loretod/Braille_Trainer/images/IMG-5150.jpg

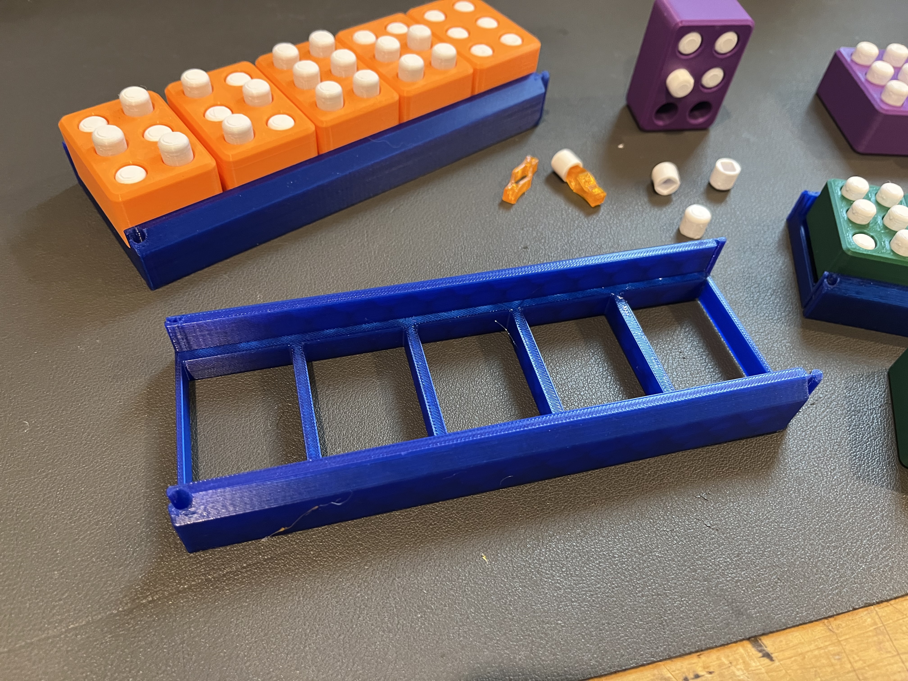
images/IMG-5150.jpg
