loretod/Braille_Trainer/images/IMG-5151.jpg

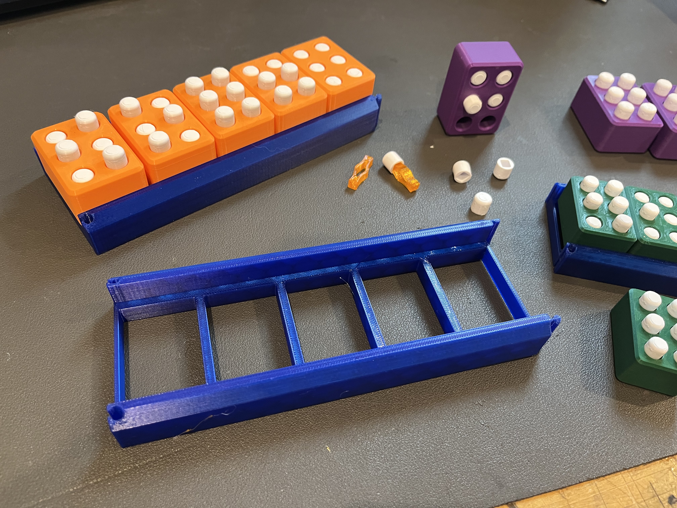
images/IMG-5151.jpg
