loretod/Braille_Trainer/images/IMG-5152.jpg

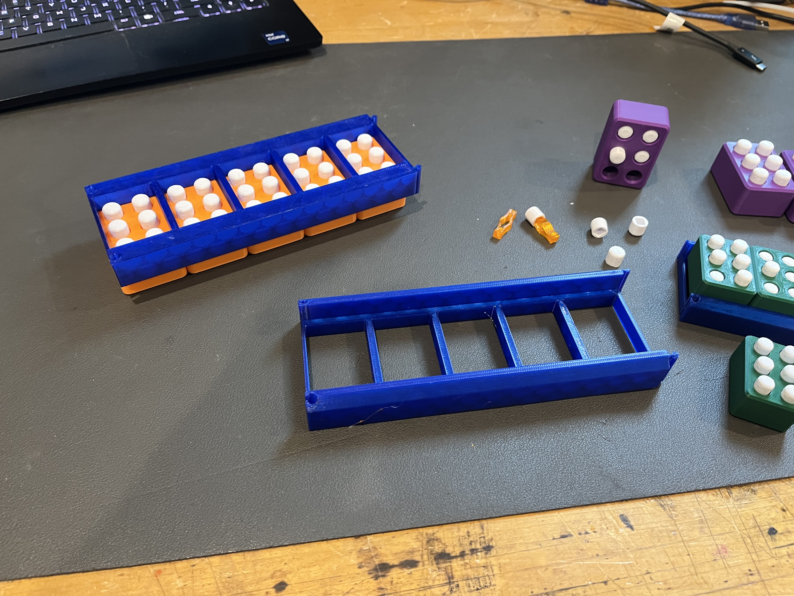
images/IMG-5152.jpg
