loretod/Braille_Trainer/images/IMG-5153.jpg

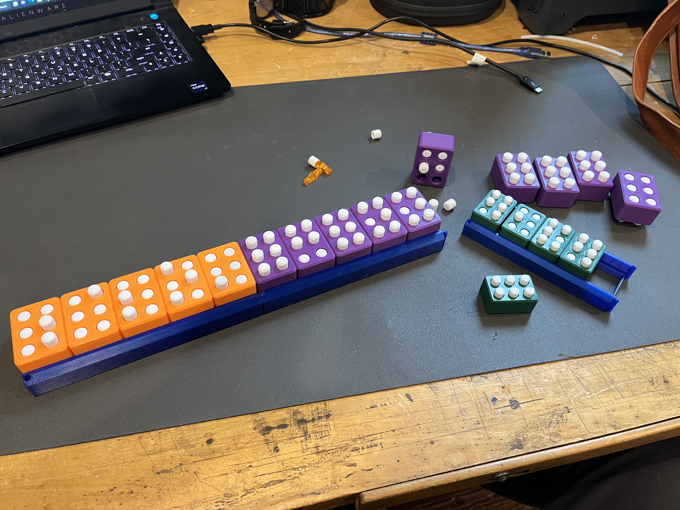
images/IMG-5153.jpg
