loretod/Braille_Trainer/images/IMG-5154.jpg

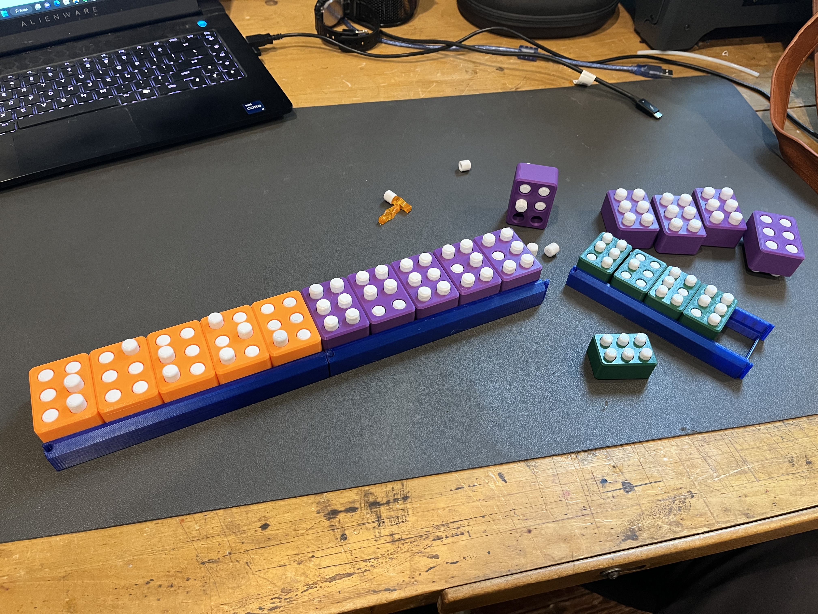
images/IMG-5154.jpg
