loretod/Braille_Trainer/images/IMG-5155.jpg

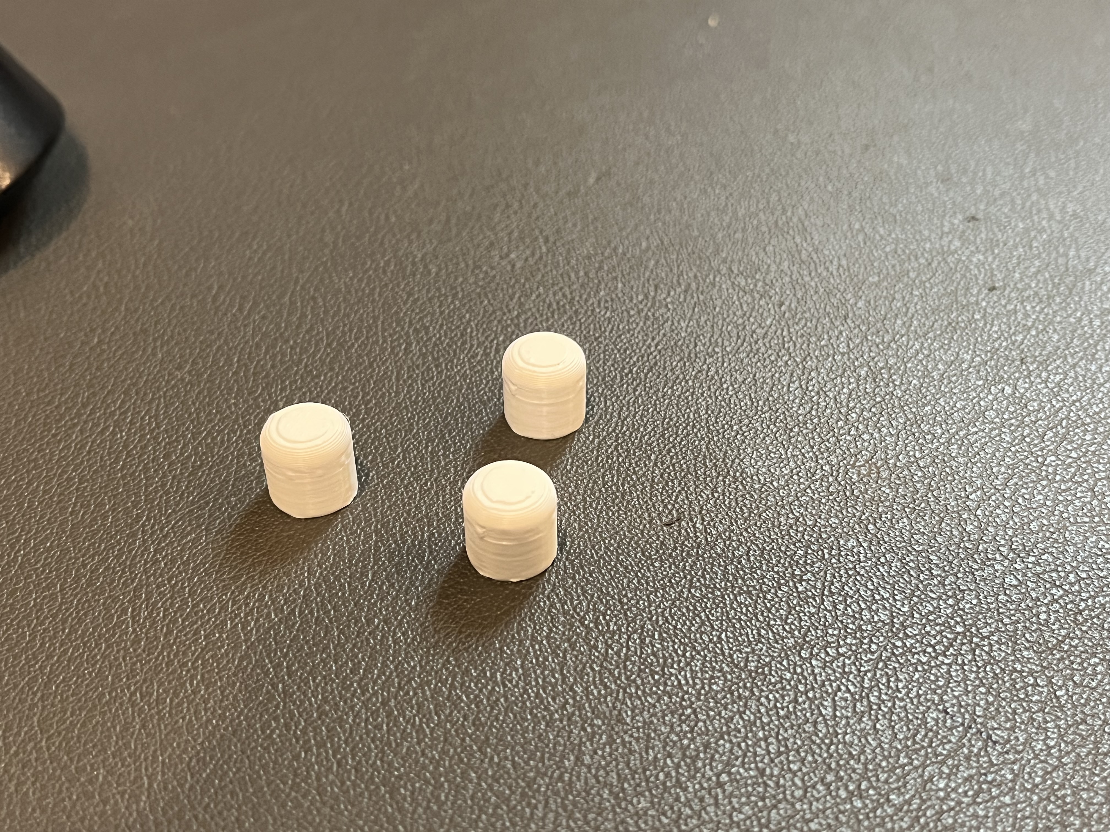
images/IMG-5155.jpg
