loretod/Braille_Trainer/images/IMG-5156.jpg

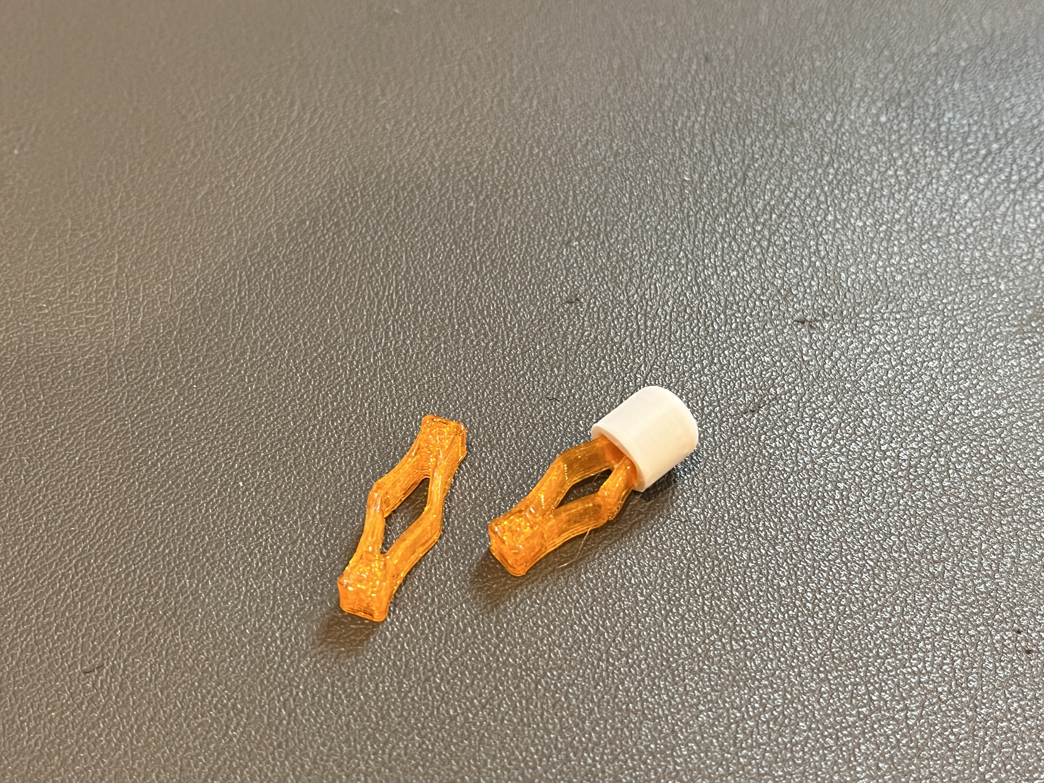
images/IMG-5156.jpg
