loretod/Braille_Trainer/images/IMG-5157.jpg

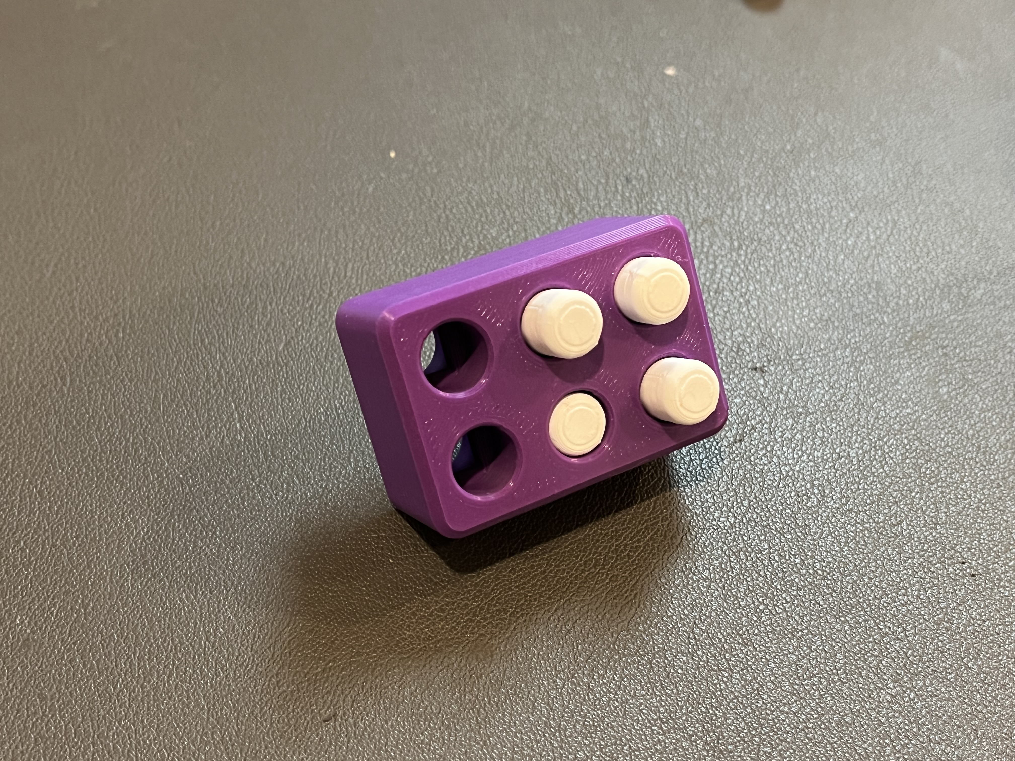
images/IMG-5157.jpg
