loretod/Braille_Trainer/images/IMG-5158.jpg

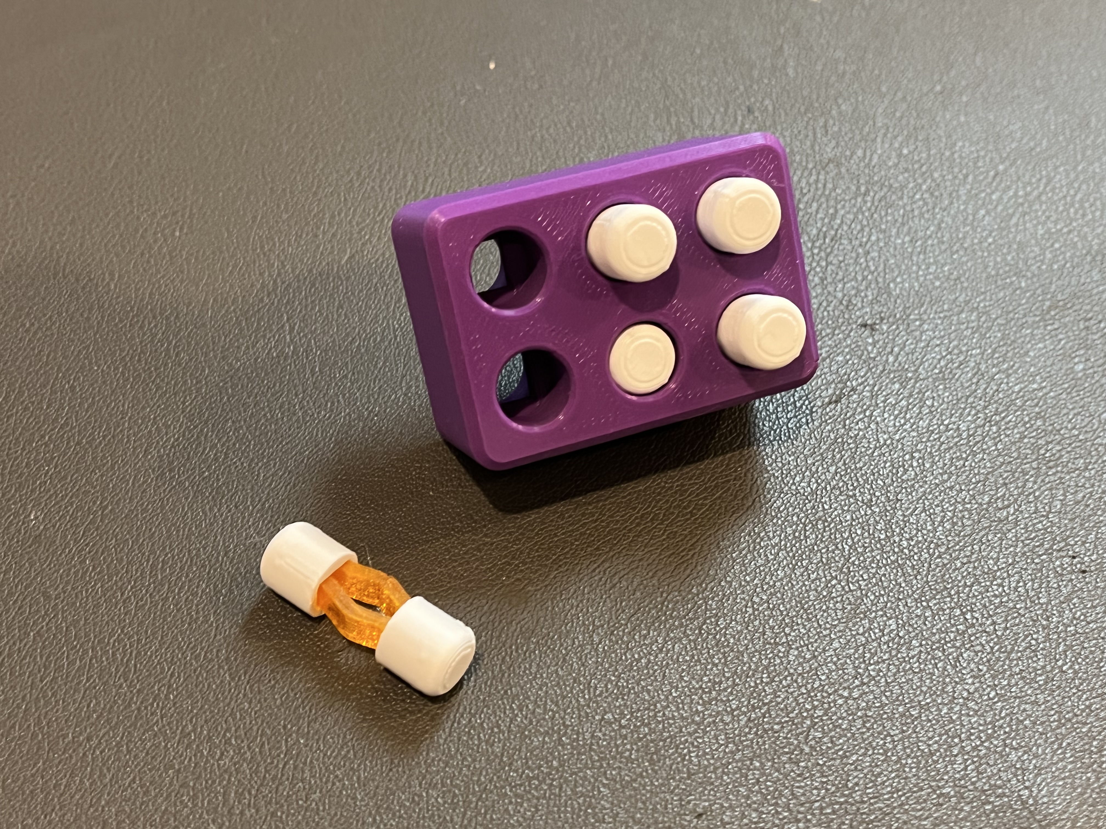
images/IMG-5158.jpg
