loretod/Braille_Trainer/images/IMG-5161.jpg

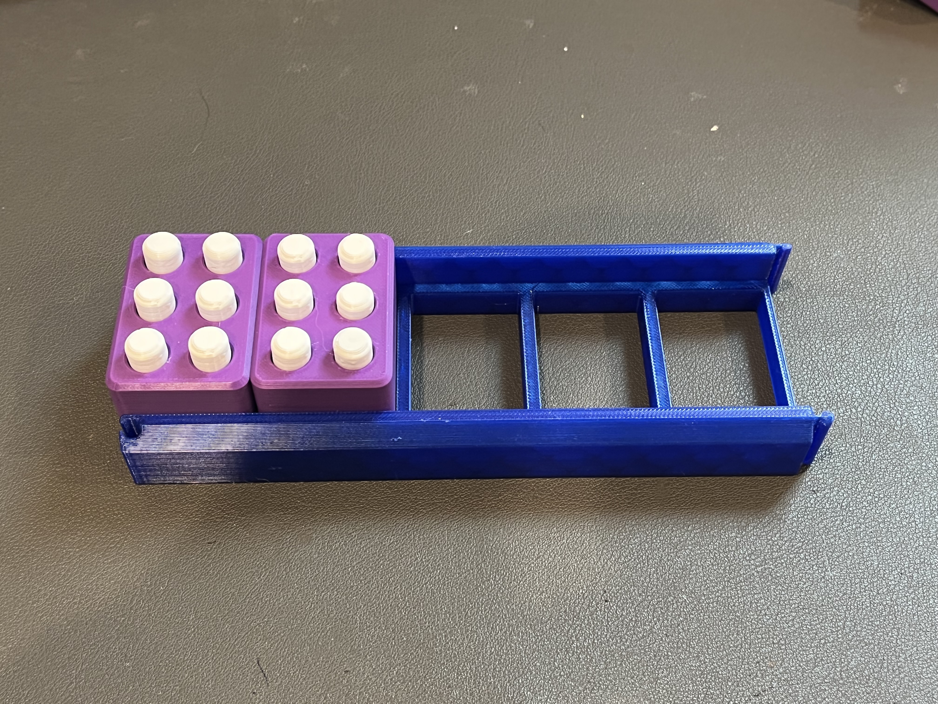
images/IMG-5161.jpg
